Elecrow-RD/CrowPanel-Pico-Display-3.5-inch-480320/example/Arduino/LibrariesPico3.5/GFX_Library_for_Arduino/examples/ImgViewer/ImgViewerAnimatedGIF/data/ezgif.com-optimize.gif

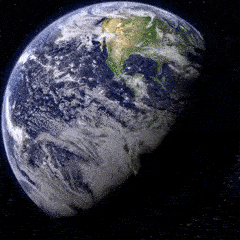
example/Arduino/LibrariesPico3.5/GFX_Library_for_Arduino/examples/ImgViewer/ImgViewerAnimatedGIF/data/ezgif.com-optimize.gif
