Elecrow-RD/CrowPanel-Pico-Display-3.5-inch-480320/example/Arduino/LibrariesPico3.5/GFX_Library_for_Arduino/examples/Sprite/SpriteGif/data/city17_240.gif

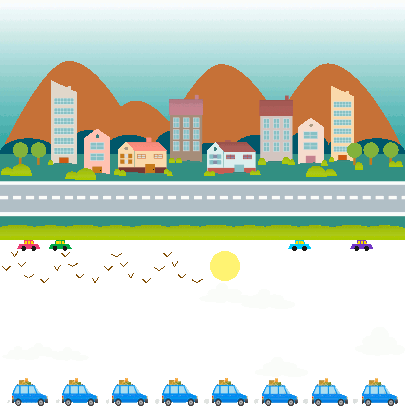
example/Arduino/LibrariesPico3.5/GFX_Library_for_Arduino/examples/Sprite/SpriteGif/data/city17_240.gif
