Elecrow-RD/CrowPanel-Pico-Display-3.5-inch-480320/example/Arduino/LibrariesPico3.5/GUIslice/docs/images/GUIslice-hier.png

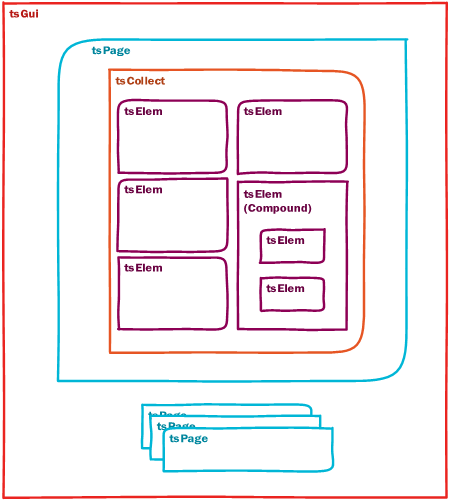
example/Arduino/LibrariesPico3.5/GUIslice/docs/images/GUIslice-hier.png
