Elecrow-RD/CrowPanel-Pico-Display-3.5-inch-480320/factory_firmware/3.jpg

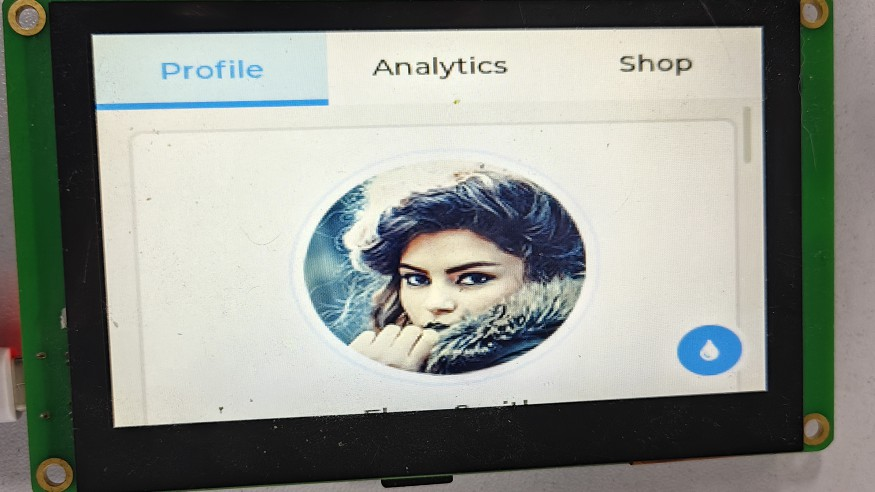
factory_firmware/3.jpg
