Elecrow-RD/CrowPanel-Pico-Display-3.5-inch-480320/example/Arduino/UI_Code&Material/3.5_UI_Material/background.png

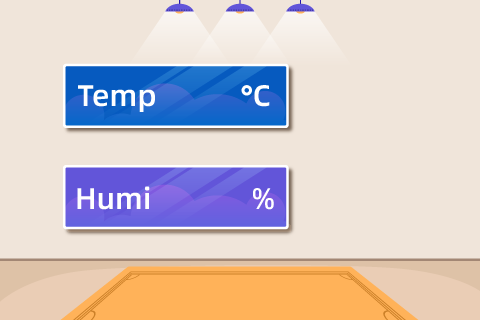
example/Arduino/UI_Code&Material/3.5_UI_Material/background.png
