Elecrow-RD/CrowPanel-Pico-Display-3.5-inch-480320/example/Arduino/LibrariesPico3.5/GUIslice/examples/builder/res/back2_24.bmp

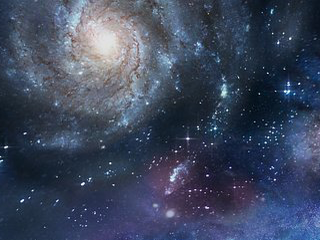
example/Arduino/LibrariesPico3.5/GUIslice/examples/builder/res/back2_24.bmp
