Elecrow-RD/CrowPanel-Pico-Display-3.5-inch-480320/example/Arduino/LibrariesPico3.5/lvgl/tests/ref_imgs/arc_1.png

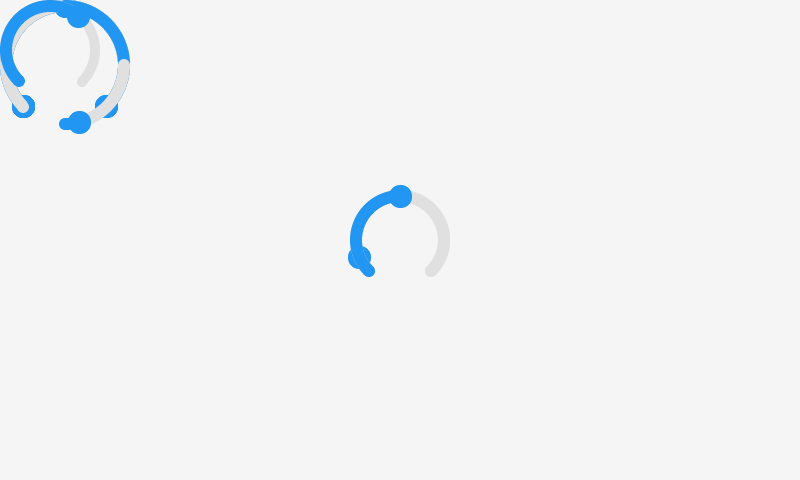
example/Arduino/LibrariesPico3.5/lvgl/tests/ref_imgs/arc_1.png
