Elecrow-RD/CrowPanel-Pico-Display-3.5-inch-480320/example/Arduino/LibrariesPico3.5/XPT2046_Touchscreen/doc/ILI9431Test.jpg

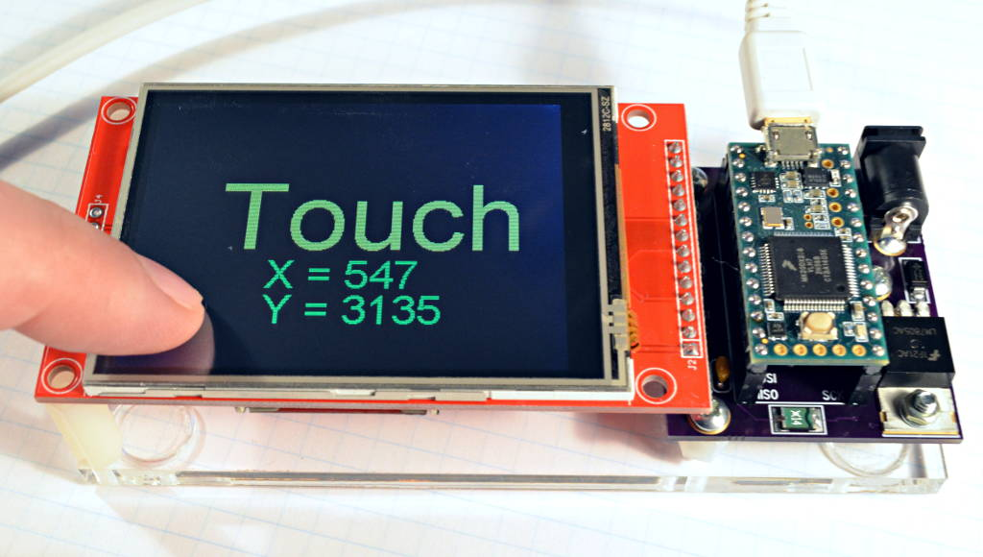
example/Arduino/LibrariesPico3.5/XPT2046_Touchscreen/doc/ILI9431Test.jpg
